Wafersat/sensor-board-design/ltc4417.kicad_sch

## KiCad design ltc4417.kicad_sch (2022-04-08)

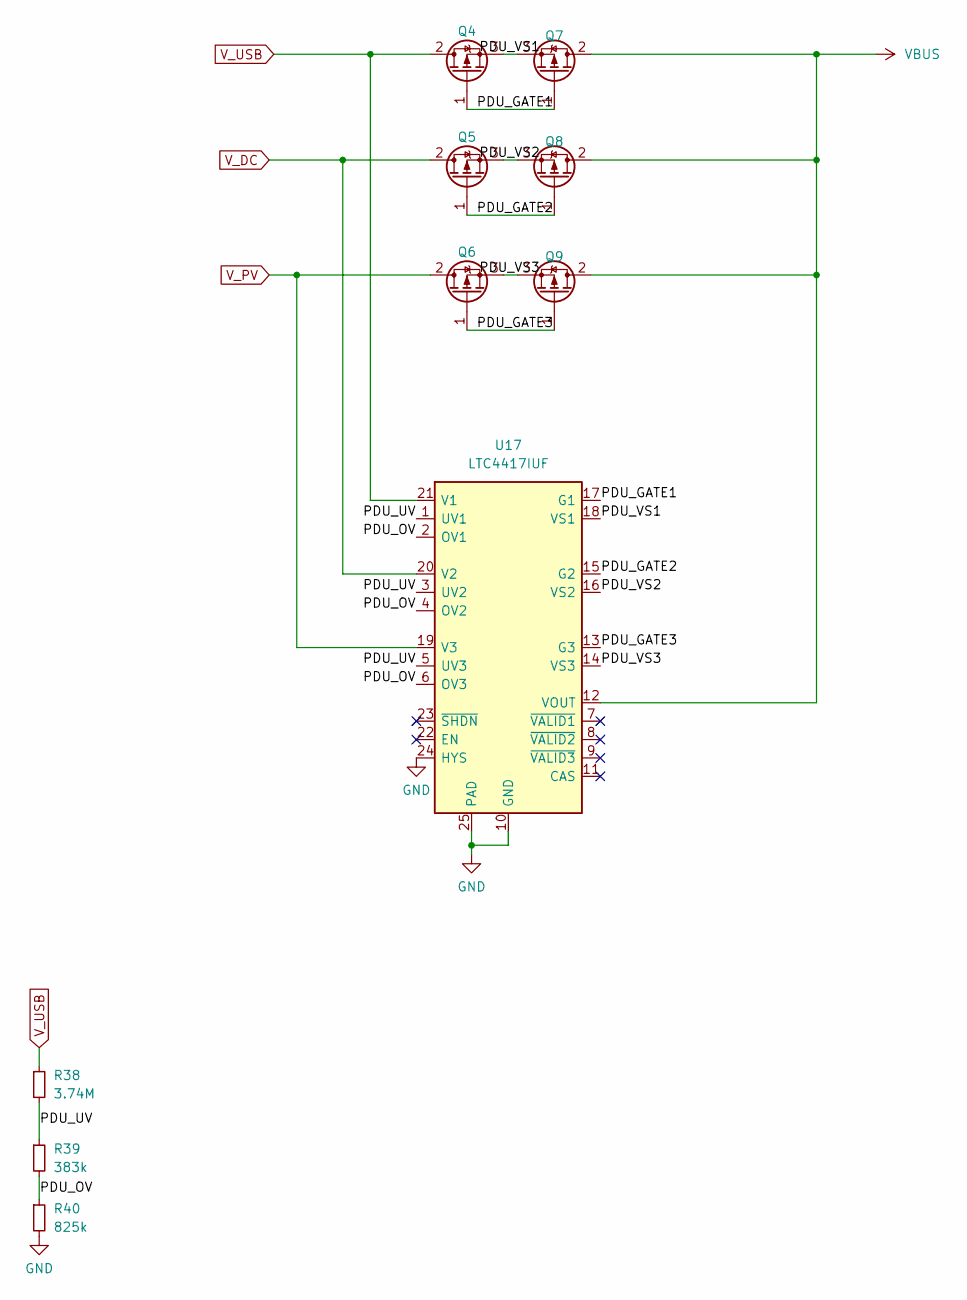
[picture p8: schematic ltc4417.kicad_sch]

Parts:
Q4, Q5, Q6, Q7, Q8, Q9: Q_PMOS_GDS; DIP-4_W7.62mm
R38: 3.74M; R_0603_1608Metric
R39: 383k; R_0603_1608Metric
R40: 825k; R_0603_1608Metric
U17: LTC4417IUF; QFN-24-1EP_4x4mm_P0.5mm_EP2.6x2.6mm

Connections:
GND: R40.2, U17.10 (GND), U17.24 (HYS), U17.25 (PAD)
unnamed: Q4.3 (S), Q7.3 (S)
unnamed: Q5.3 (S), Q8.3 (S)
unnamed: Q6.3 (S), Q9.3 (S)
PDU_GATE1: Q4.1 (G), Q7.1 (G), U17.17 (G1)
PDU_GATE2: Q5.1 (G), Q8.1 (G), U17.15 (G2)
PDU_GATE3: Q6.1 (G), Q9.1 (G), U17.13 (G3)
PDU_OV: R39.2, R40.1, U17.2 (OV1), U17.4 (OV2), U17.6 (OV3)
PDU_UV: R38.2, R39.1, U17.1 (UV1), U17.3 (UV2), U17.5 (UV3)
PDU_VS1: U17.18 (VS1)
PDU_VS2: U17.16 (VS2)
PDU_VS3: U17.14 (VS3)
VBUS: Q7.2 (D), Q8.2 (D), Q9.2 (D), U17.12 (VOUT)
V_DC: Q5.2 (D), U17.20 (V2)
V_PV: Q6.2 (D), U17.19 (V3)
V_USB: Q4.2 (D), R38.1, U17.21 (V1)
