Wafersat/sensor-board-design/pdu.kicad_sch

## KiCad design pdu.kicad_sch (2022-04-08)

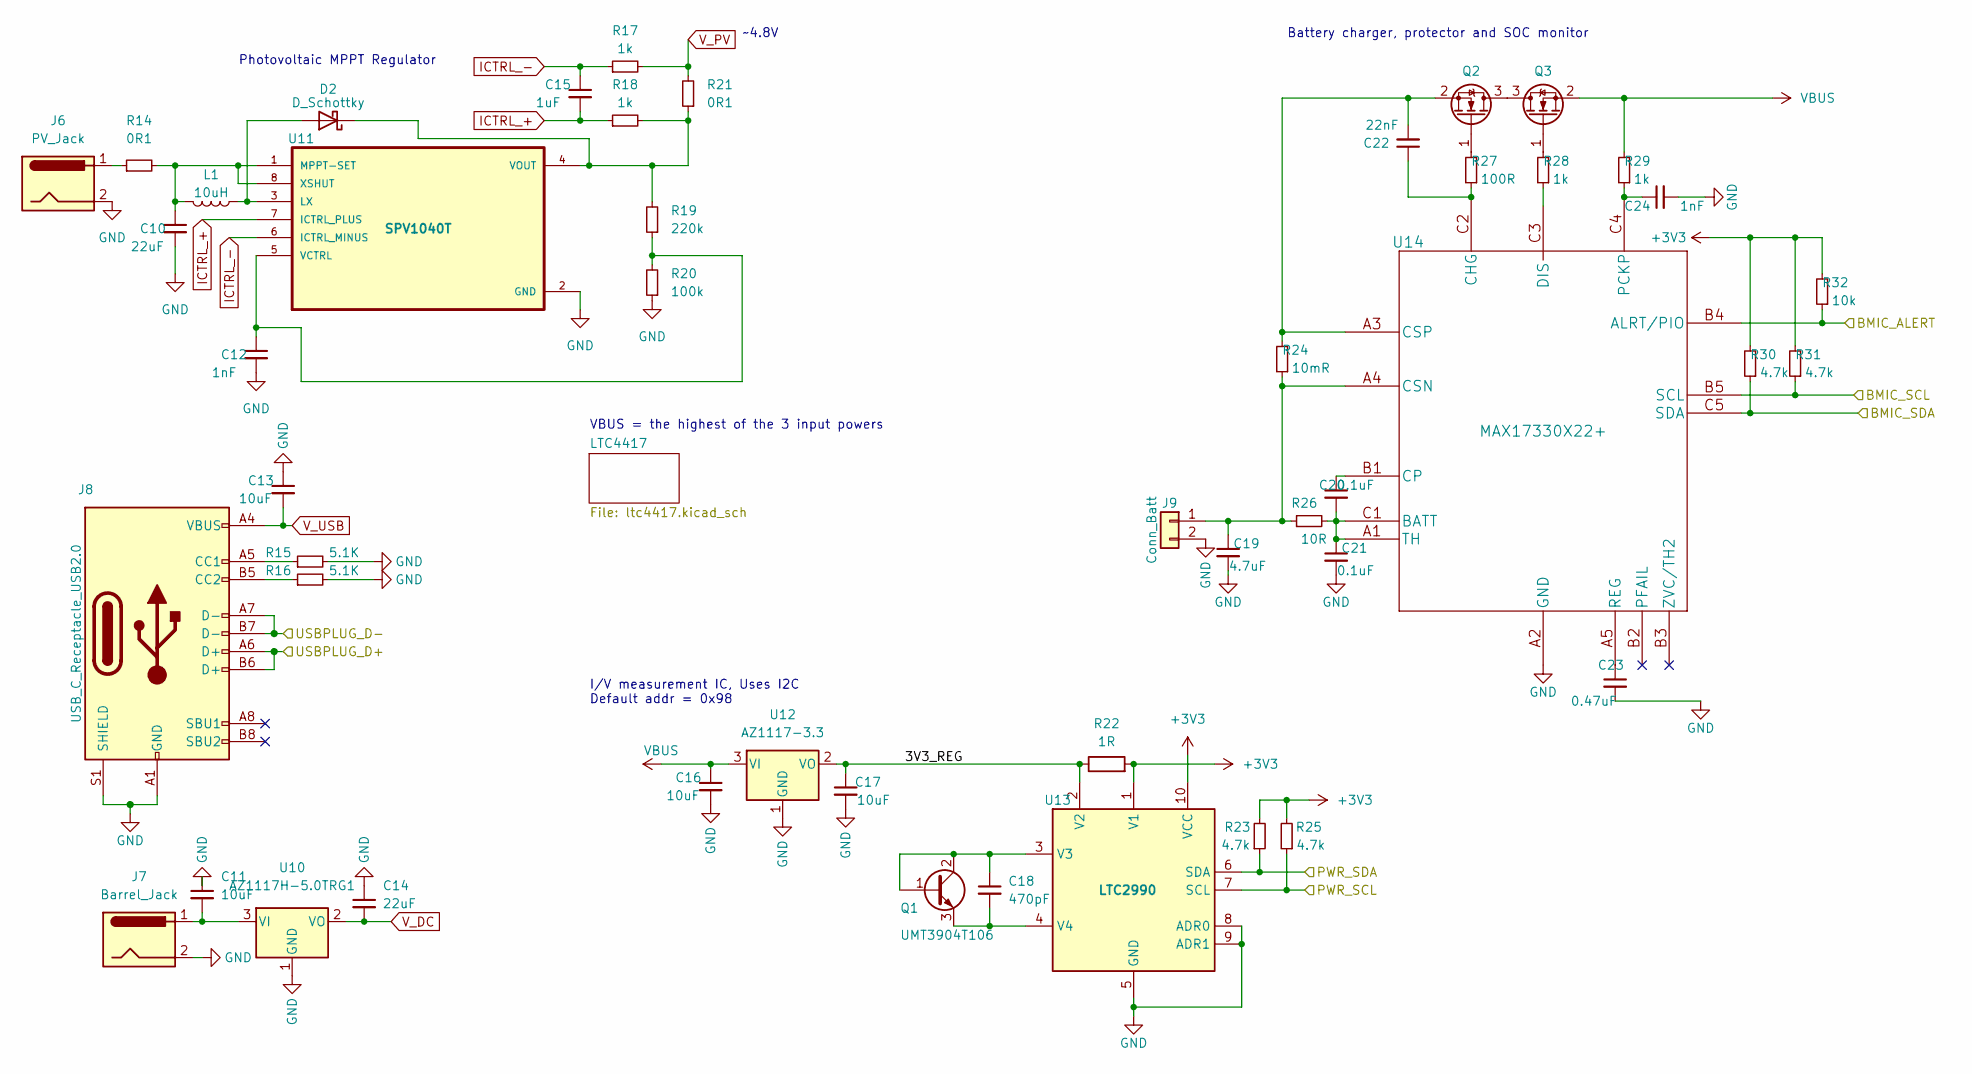
[picture p9: schematic pdu.kicad_sch]

Parts:
C10, C14: 22uF; C_0603_1608Metric
C11, C13, C16, C17: 10uF; C_0603_1608Metric
C12, C24: 1nF; C_0603_1608Metric
C15: 1uF; C_0603_1608Metric
C18: 470pF; C_0603_1608Metric
C19: 4.7uF; C_0603_1608Metric
C20, C21: 0.1uF; C_0603_1608Metric
C22: 22nF; C_0603_1608Metric
C23: 0.47uF; C_0603_1608Metric
D2: D_Schottky; D_0603_1608Metric
J6: PV_Jack; BarrelJack_Horizontal
J7: Barrel_Jack; BarrelJack_Horizontal
J8: USB_C_Receptacle_USB2.0; USB_C_Receptacle_XKB_U262-16XN-4BVC11; LCSC C319148
J9: Conn_Batt; JST_PH_S2B-PH-SM4-TB_1x02-1MP_P2.00mm_Horizontal; LCSC C47647
L1: 10uH; L_0603_1608Metric
Q1: UMT3904T106; SOT65P210X100-3N
Q2, Q3: DMG3414U; SOT-23
R14, R21: 0R1; R_0603_1608Metric
R15, R16: 5.1K; R_0603_1608Metric
R17, R18, R28, R29: 1k; R_0603_1608Metric
R19: 220k; R_0603_1608Metric
R20: 100k; R_0603_1608Metric
R22: 1R; R_0603_1608Metric
R23, R25, R30, R31: 4.7k; R_0603_1608Metric
R24: 10mR; R_0603_1608Metric
R26: 10R; R_0603_1608Metric
R27: 100R; R_0603_1608Metric
R32: 10k; R_0603_1608Metric
U10: AZ1117H-5.0TRG1; SOT-223
U11: SPV1040T; SOP65P640X120-8N; PARTREV 7
U12: AZ1117-3.3; SOT-223
U13: LTC2990; MSOP-10_3x3mm_P0.5mm
U14: MAX17330X22+; MAX17330X22&plus_

Connections:
3V3_REG: C17.1, R22.1, U12.2 (VO), U13.2 (V2)
+3V3: R22.2, R23.2, R25.2, R30.2, R31.2, R32.2, U13.1 (V1), U13.10 (VCC)
BMIC_ALERT: R32.1, U14.B4 (ALRT/PIO)
BMIC_SCL: R31.1, U14.B5 (SCL)
BMIC_SDA: R30.1, U14.C5 (SDA)
GND: C10.2, C11.1, C12.2, C13.1, C14.1, C16.2, C17.2, C19.2, C21.2, C23.2, C24.2, J6.2, J7.2, J8.A1 (GND), J8.A12 (GND), J8.B1 (GND), J8.B12 (GND), J8.S1 (SHIELD), J9.2, R15.2, R16.2, R20.1, U10.1 (GND), U11.2 (GND), U12.1 (GND), U13.5 (GND), U13.8 (ADR0), U13.9 (ADR1), U14.A2 (GND)
ICTRL_+: C15.2, R18.1, U11.7 (ICTRL_PLUS)
ICTRL_-: C15.1, R17.1, U11.6 (ICTRL_MINUS)
unnamed: C10.1, L1.2, R14.2, U11.1 (MPPT-SET), U11.8 (XSHUT)
unnamed: C11.2, J7.1, U10.3 (VI)
unnamed: C12.1, R19.1, R20.2, U11.5 (VCTRL)
unnamed: C18.1, Q1.1 (B), Q1.2 (C), U13.3 (V3)
unnamed: C18.2, Q1.3 (E), U13.4 (V4)
unnamed: C19.1, J9.1, R24.1, R26.1, U14.A4 (CSN)
unnamed: C20.1, U14.B1 (CP)
unnamed: C20.2, C21.1, R26.2, U14.A1 (TH), U14.C1 (BATT)
unnamed: C22.1, R27.1, U14.C2 (CHG)
unnamed: C22.2, Q2.2 (S), R24.2, U14.A3 (CSP)
unnamed: C23.1, U14.A5 (REG)
unnamed: C24.1, R29.1, U14.C4 (PCKP)
unnamed: D2.1 (K), R18.2, R19.2, R21.1, U11.4 (VOUT)
unnamed: D2.2 (A), L1.1, U11.3 (LX)
unnamed: J6.1, R14.1
unnamed: J8.A5 (CC1), R15.1
unnamed: J8.B5 (CC2), R16.1
unnamed: Q2.1 (G), R27.2
unnamed: Q2.3 (D), Q3.3 (D)
unnamed: Q3.1 (G), R28.2
unnamed: R28.1, U14.C3 (DIS)
PWR_SCL: R25.1, U13.7 (SCL)
PWR_SDA: R23.1, U13.6 (SDA)
USBPLUG_D+: J8.A6 (D+), J8.B6 (D+)
USBPLUG_D-: J8.A7 (D-), J8.B7 (D-)
VBUS: C16.1, Q3.2 (S), R29.2, U12.3 (VI)
V_DC: C14.2, U10.2 (VO)
V_PV: R17.2, R21.2
V_USB: C13.2, J8.A4 (VBUS), J8.A9 (VBUS), J8.B4 (VBUS), J8.B9 (VBUS)

Notes on the sheet:
I/V measurement IC, Uses I2C Default addr = 0x98
VBUS = the highest of the 3 input powers
Photovoltaic MPPT Regulator
Battery charger, protector and SOC monitor
~4.8V
