Wafersat/sensor-board-design/rp2040.kicad_sch

## KiCad design rp2040.kicad_sch (2022-04-08)

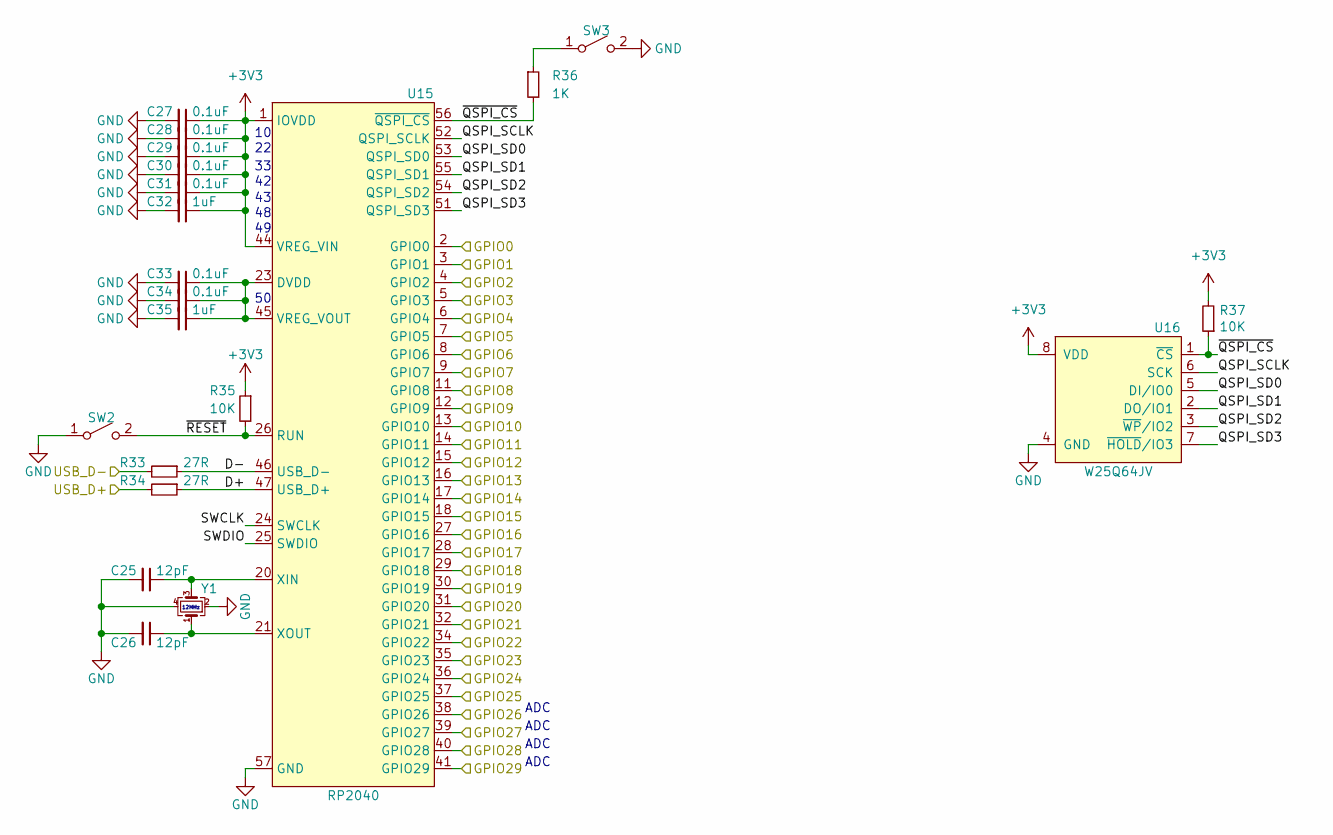
[picture p10: schematic rp2040.kicad_sch]

Parts:
C25, C26: 12pF; C_0603_1608Metric
C27, C28, C29, C30, C31, C33, C34: 0.1uF; C_0603_1608Metric
C32, C35: 1uF; C_0603_1608Metric
R33, R34: 27R; R_0603_1608Metric
R35, R37: 10K; R_0603_1608Metric
R36: 1K; R_0603_1608Metric
SW2: SW_RESET; SW_SPST_B3U-1000P
SW3: SW_BOOTSEL; SW_SPST_B3U-1000P
U15: RP2040; QFN40P700X700X90-57N
U16: W25Q64JV; WSON-8-1EP_6x5mm_P1.27mm_EP3.4x4mm
Y1: XYDBPCNANF-12MHZ; Crystal_SMD_2520-4Pin_2.5x2.0mm; LCSC C521567

Connections:
+3V3: C27.1, C28.1, C29.1, C30.1, C31.1, C32.1, R35.1, R37.2, U15.1 (IOVDD), U15.10 (IOVDD), U15.22 (IOVDD), U15.33 (IOVDD), U15.42 (IOVDD), U15.43 (ADC_AVDD), U15.44 (VREG_VIN), U15.48 (USB_VDD), U15.49 (IOVDD), U16.8 (VDD)
D+: R34.1, U15.47 (USB_D+)
D-: R33.1, U15.46 (USB_D-)
GND: C25.2, C26.2, C27.2, C28.2, C29.2, C30.2, C31.2, C32.2, C33.2, C34.2, C35.2, SW2.1 (A), SW3.2 (B), U15.19 (TESTEN), U15.57 (GND), U16.4 (GND), U16.9 (GND), Y1.2, Y1.4
GPIO0: U15.2 (GPIO0)
GPIO1: U15.3 (GPIO1)
GPIO2: U15.4 (GPIO2)
GPIO3: U15.5 (GPIO3)
GPIO4: U15.6 (GPIO4)
GPIO5: U15.7 (GPIO5)
GPIO6: U15.8 (GPIO6)
GPIO7: U15.9 (GPIO7)
GPIO8: U15.11 (GPIO8)
GPIO9: U15.12 (GPIO9)
GPIO10: U15.13 (GPIO10)
GPIO11: U15.14 (GPIO11)
GPIO12: U15.15 (GPIO12)
GPIO13: U15.16 (GPIO13)
GPIO14: U15.17 (GPIO14)
GPIO15: U15.18 (GPIO15)
GPIO16: U15.27 (GPIO16)
GPIO17: U15.28 (GPIO17)
GPIO18: U15.29 (GPIO18)
GPIO19: U15.30 (GPIO19)
GPIO20: U15.31 (GPIO20)
GPIO21: U15.32 (GPIO21)
GPIO22: U15.34 (GPIO22)
GPIO23: U15.35 (GPIO23)
GPIO24: U15.36 (GPIO24)
GPIO25: U15.37 (GPIO25)
GPIO26: U15.38 (GPIO26)
GPIO27: U15.39 (GPIO27)
GPIO28: U15.40 (GPIO28)
GPIO29: U15.41 (GPIO29)
unnamed: C25.1, U15.20 (XIN), Y1.3
unnamed: C26.1, U15.21 (XOUT), Y1.1
unnamed: C33.1, C34.1, C35.1, U15.23 (DVDD), U15.45 (VREG_VOUT), U15.50 (DVDD)
unnamed: R36.1, SW3.1 (A)
QSPI_SCLK: U15.52 (QSPI_SCLK), U16.6 (SCK)
QSPI_SD0: U15.53 (QSPI_SD0), U16.5 (DI/IO0)
QSPI_SD1: U15.55 (QSPI_SD1), U16.2 (DO/IO1)
QSPI_SD2: U15.54 (QSPI_SD2), U16.3 (~WP/IO2)
QSPI_SD3: U15.51 (QSPI_SD3), U16.7 (~HOLD/IO3)
SWCLK: U15.24 (SWCLK)
SWDIO: U15.25 (SWDIO)
USB_D+: R34.2
USB_D-: R33.2
~QSPI_CS: R36.2, R37.1, U15.56 (~QSPI_CS), U16.1 (~CS)
~RESET: R35.2, SW2.2 (B), U15.26 (RUN)

Notes on the sheet:
12MHz
ADC
