Wafersat/sensor-board-design/sensors.kicad_sch

## KiCad design sensors.kicad_sch (2022-04-08)

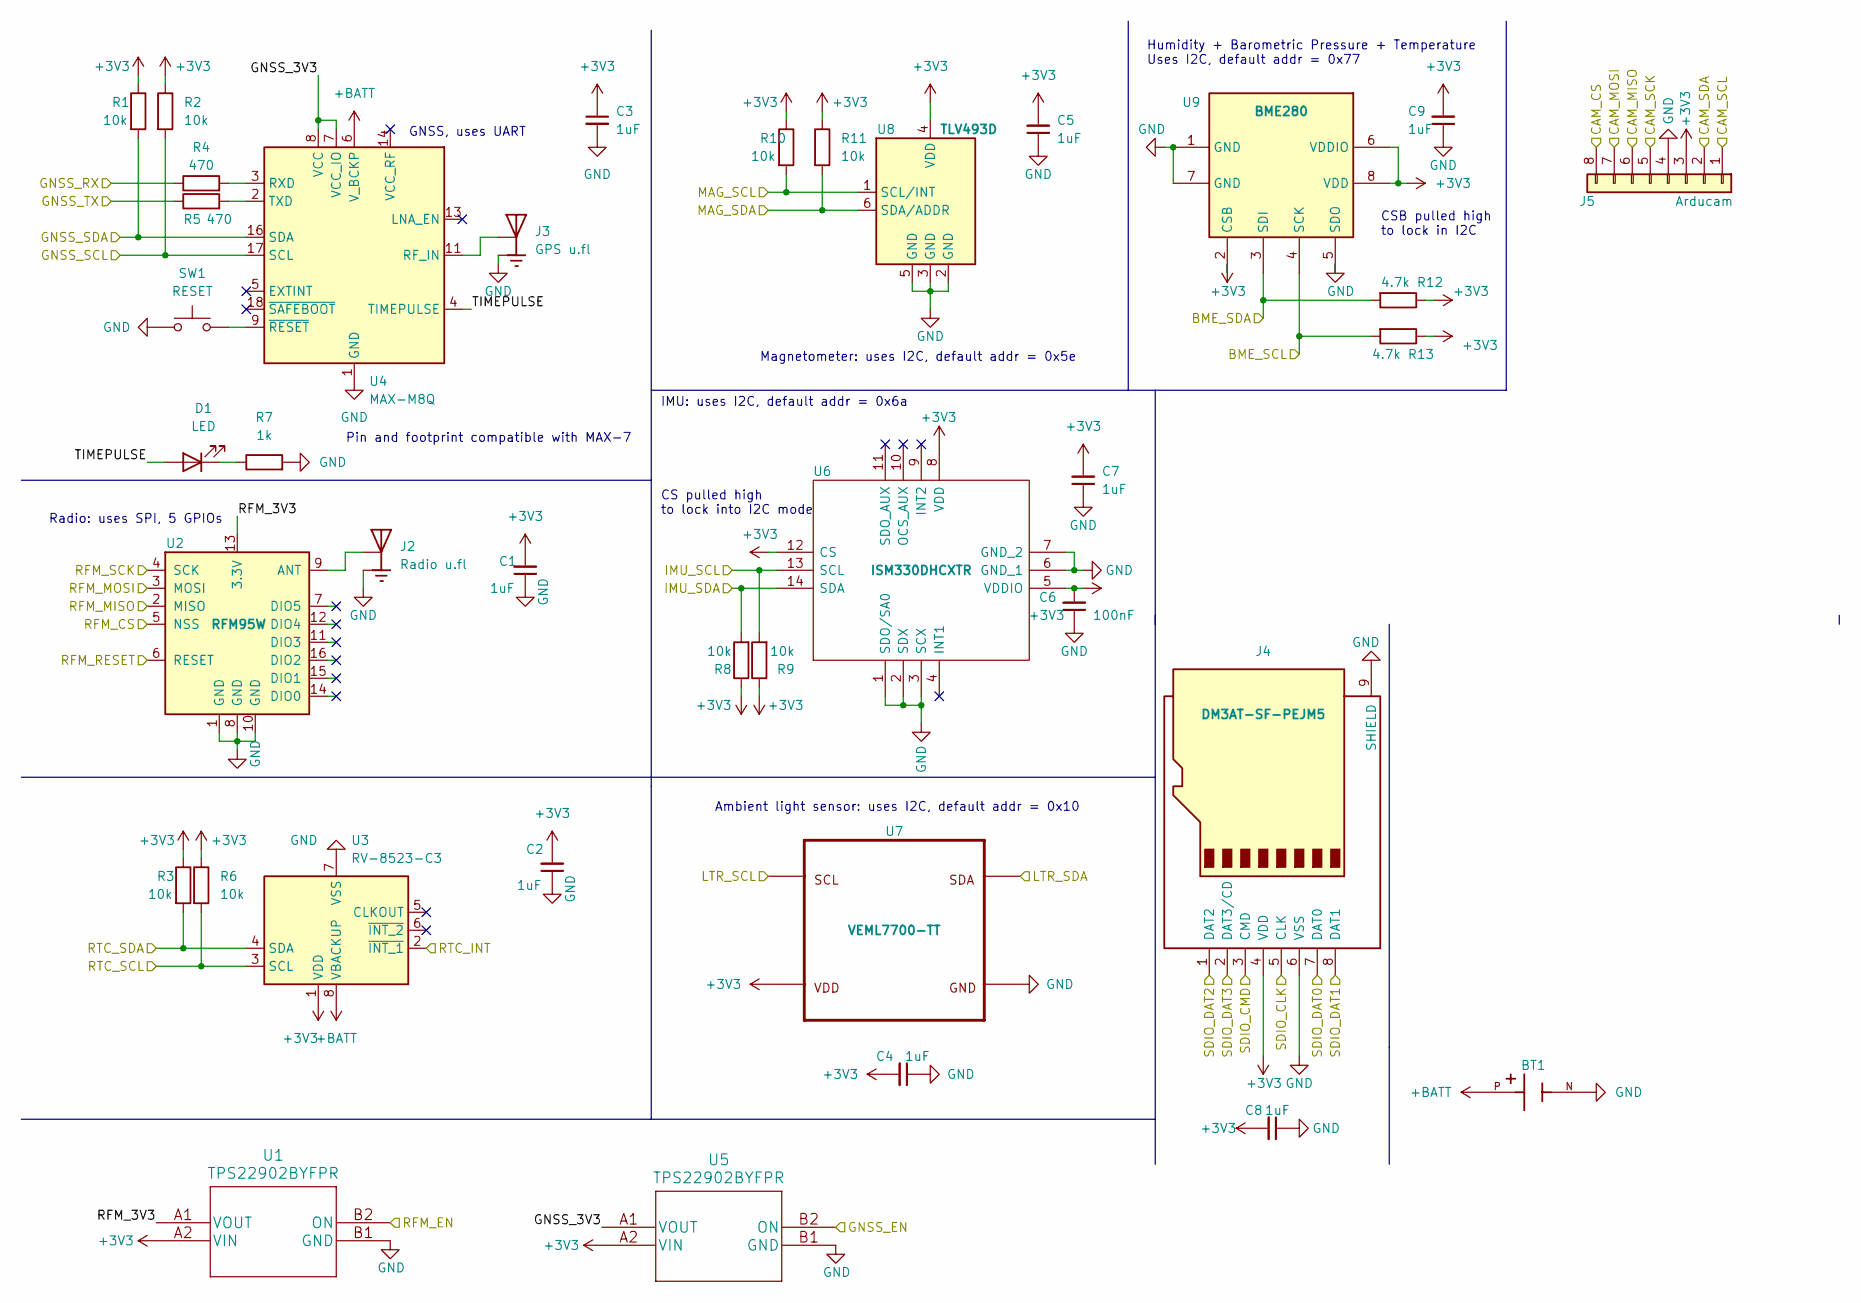
[picture p11: schematic sensors.kicad_sch]

Parts:
BT1: S8411-45R; BAT_S8411-45R
C1, C2, C3, C4, C5, C7, C8, C9: 1uF; C_0603_1608Metric
C6: 100nF; C_0603_1608Metric
D1: LED; LED_0603_1608Metric
J2: Radio u.fl; HRS_U.FL-R-SMT-1(10)
J3: GPS u.fl; HRS_U.FL-R-SMT-1(10)
J4: DM3AT-SF-PEJM5; HRS_DM3AT-SF-PEJM5
J5: Arducam; PinHeader_1x08_P2.54mm_Vertical
R1, R2, R3, R6, R8, R9, R10, R11: 10k; R_0603_1608Metric
R4, R5: 470; R_0603_1608Metric
R7: 1k; R_0603_1608Metric
R12, R13: 4.7k; R_0603_1608Metric
SW1: RESET; SW_Push_SPST_NO_Alps_SKRK
U1, U5: TPS22902BYFPR
U2: RFM95W; XCVR_RFM95W-915S2
U3: RV-8523-C3; RTC_SMD_MicroCrystal_C3_2.5x3.7mm
U4: MAX-M8Q; ublox_MAX
U6: ISM330DHCXTR; LGA-14_2.5X3X0.86_; Manufacturer_Part_Number ISM330DHCXTR; Mouser Part Number 511-ISM330DHCXTR
U7: VEML7700-TT; XDCR_VEML7700-TT; PARTREV 1.3
U8: TLV493D; SOT-23-6
U9: BME280; Bosch_LGA-8_2.5x2.5mm_P0.65mm_ClockwisePinNumbering

Connections:
+3V3: C1.2, C2.2, C3.1, C4.2, C5.2, C6.2, C7.2, C8.2, C9.2, J4.4 (VDD), J5.3, R1.1, R2.1, R3.1, R6.1, R8.1, R9.1, R10.1, R11.1, R12.1, R13.1, U1.A2 (VIN), U3.1 (VDD), U5.A2 (VIN), U6.5 (VDDIO), U6.8 (VDD), U6.12 (CS), U7.2, U8.4 (VDD), U9.2 (CSB), U9.6 (VDDIO), U9.8 (VDD)
+BATT: BT1.P, U3.8 (VBACKUP), U4.6 (V_BCKP)
BME_SCL: R13.2, U9.4 (SCK)
BME_SDA: R12.2, U9.3 (SDI)
CAM_CS: J5.8
CAM_MISO: J5.6
CAM_MOSI: J5.7
CAM_SCK: J5.5
CAM_SCL: J5.1
CAM_SDA: J5.2
GND: BT1.N, C1.1, C2.1, C3.2, C4.1, C5.1, C6.1, C7.1, C8.1, C9.1, J2.1, J2.3, J3.1, J3.3, J4.6 (VSS), J4.9 (SHIELD), J5.4, R7.2, SW1.1, U1.B1 (GND), U2.1 (GND), U2.8 (GND), U2.10 (GND), U3.7 (VSS), U4.1 (GND), U4.10 (GND), U4.12 (GND), U5.B1 (GND), U6.1 (SDO/SA0), U6.2 (SDX), U6.3 (SCX), U6.6 (GND_1), U6.7 (GND_2), U7.3, U8.2 (GND), U8.3 (GND), U8.5 (GND), U9.1 (GND), U9.5 (SDO), U9.7 (GND)
GNSS_3V3: U4.7 (VCC_IO), U4.8 (VCC), U5.A1 (VOUT)
GNSS_EN: U5.B2 (ON)
GNSS_RX: R4.1
GNSS_SCL: R2.2, U4.17 (SCL)
GNSS_SDA: R1.2, U4.16 (SDA)
GNSS_TX: R5.1
IMU_SCL: R9.2, U6.13 (SCL)
IMU_SDA: R8.2, U6.14 (SDA)
LTR_SCL: U7.1
LTR_SDA: U7.4
MAG_SCL: R10.2, U8.1 (SCL/INT)
MAG_SDA: R11.2, U8.6 (SDA/ADDR)
unnamed: D1.1 (K), R7.1
unnamed: J2.2, U2.9 (ANT)
unnamed: J3.2, U4.11 (RF_IN)
unnamed: R4.2, U4.3 (RXD)
unnamed: R5.2, U4.2 (TXD)
unnamed: SW1.2, U4.9 (~RESET)
RFM_3V3: U1.A1 (VOUT), U2.13 (3.3V)
RFM_CS: U2.5 (NSS)
RFM_EN: U1.B2 (ON)
RFM_MISO: U2.2 (MISO)
RFM_MOSI: U2.3 (MOSI)
RFM_RESET: U2.6 (RESET)
RFM_SCK: U2.4 (SCK)
RTC_INT: U3.2 (~INT_1)
RTC_SCL: R6.2, U3.3 (SCL)
RTC_SDA: R3.2, U3.4 (SDA)
SDIO_CLK: J4.5 (CLK)
SDIO_CMD: J4.3 (CMD)
SDIO_DAT0: J4.7 (DAT0)
SDIO_DAT1: J4.8 (DAT1)
SDIO_DAT2: J4.1 (DAT2)
SDIO_DAT3: J4.2 (DAT3/CD)
TIMEPULSE: D1.2 (A), U4.4 (TIMEPULSE)

Notes on the sheet:
Humidity + Barometric Pressure + Temperature Uses I2C, default addr = 0x77
Ambient light sensor: uses I2C, default addr = 0x10
Pin and footprint compatible with MAX-7
CS pulled high to lock into I2C mode
Radio: uses SPI, 5 GPIOs
CSB pulled high to lock in I2C
Magnetometer: uses I2C, default addr = 0x5e
GNSS, uses UART
IMU: uses I2C, default addr = 0x6a
